Kampi/Watch-DevKit-HW/production/watch-dk-PRELIMINARY/HTML/images/cat_pdf_drill_map_ZSWatch-Watch-DevKit-PTH_drill_map.png

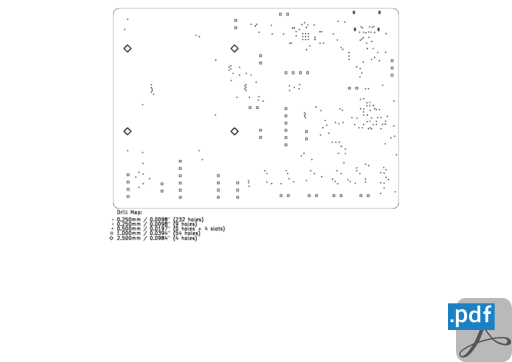
production/watch-dk-PRELIMINARY/HTML/images/cat_pdf_drill_map_ZSWatch-Watch-DevKit-PTH_drill_map.png
