Kampi/Watch-DevKit-HW/production/watch-dk-PRELIMINARY/HTML/images/cat_pdf_schematic_ZSWatch-Watch-DevKit-schematic.png

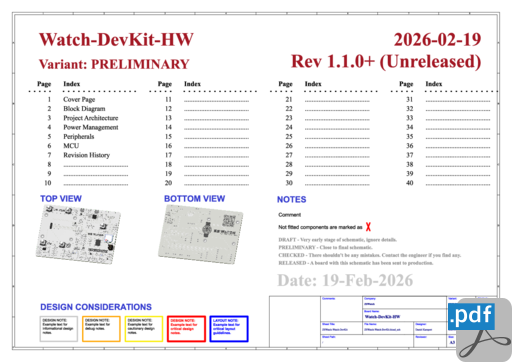
production/watch-dk-PRELIMINARY/HTML/images/cat_pdf_schematic_ZSWatch-Watch-DevKit-schematic.png
