Kampi/Watch-DevKit-HW/production/watch-dk-PRELIMINARY/HTML/images/cat_png_3d_viewer_bottom_ZSWatch-Watch-DevKit-bottom.png

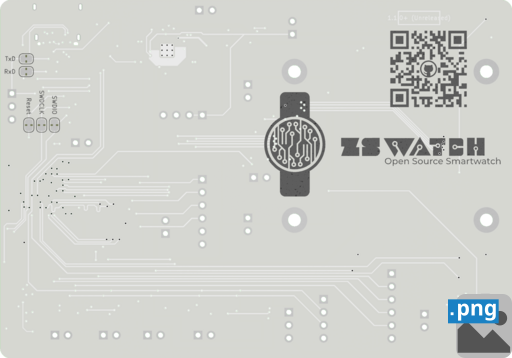
production/watch-dk-PRELIMINARY/HTML/images/cat_png_3d_viewer_bottom_ZSWatch-Watch-DevKit-bottom.png
