Kampi/Watch-DevKit-HW/production/watch-dk-PRELIMINARY/Images/ZSWatch-Watch-DevKit-bottom.png

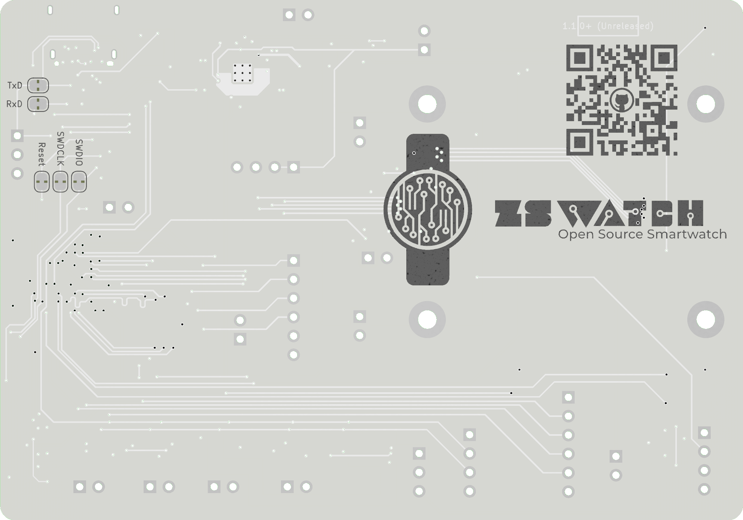
production/watch-dk-PRELIMINARY/Images/ZSWatch-Watch-DevKit-bottom.png
