Kampi/Watch-DevKit-HW/production/watch-dk-RELEASED/HTML/images/cat_png_3d_viewer_bottom_ZSWatch-Watch-DevKit-bottom.png

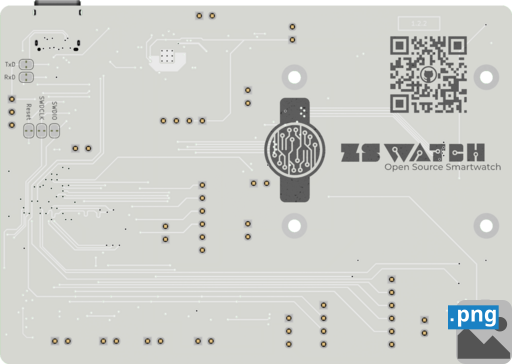
production/watch-dk-RELEASED/HTML/images/cat_png_3d_viewer_bottom_ZSWatch-Watch-DevKit-bottom.png
