Kampi/Watch-DevKit-HW/production/watch-dk-RELEASED/HTML/images/cat_png_3d_viewer_top_ZSWatch-Watch-DevKit-top.png

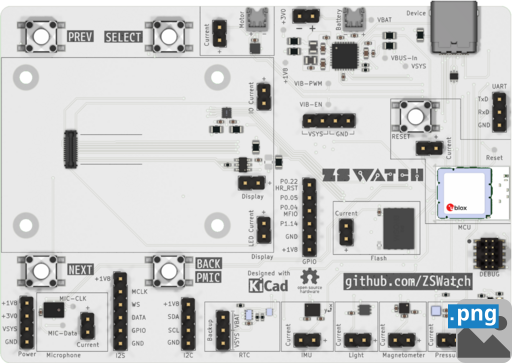
production/watch-dk-RELEASED/HTML/images/cat_png_3d_viewer_top_ZSWatch-Watch-DevKit-top.png
