Kampi/Watch-DevKit-HW/production/watch-dk-RELEASED/Images/ZSWatch-Watch-DevKit-bottom.png

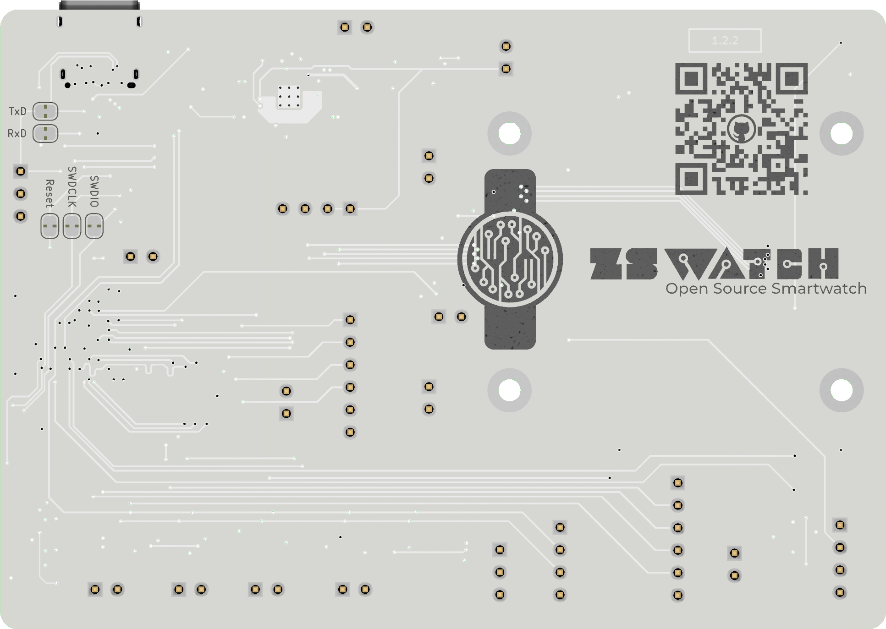
production/watch-dk-RELEASED/Images/ZSWatch-Watch-DevKit-bottom.png
