Kampi/Watch-DevKit-HW/production/watch-dk-PRELIMINARY/Manufacturing/Fabrication/Drill Tables/ZSWatch-Watch-DevKit-(L1-L4)_NPTH_drill_table.csv

Count | Hole Size | Plated | Hole Shape | Drill Layer Pair | Hole Type
1 + 1 | 0.65mm (25.59mils) | NPTH | Round + Slot | F.Cu - B.Cu | Mechanical
Total 2
