Kampi/Watch-DevKit-HW/production/watch-dk-PRELIMINARY/HTML/images/cat_pdf_fabrication_ZSWatch-Watch-DevKit-fabrication.png

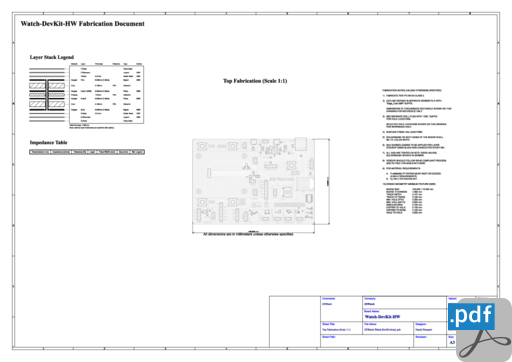
production/watch-dk-PRELIMINARY/HTML/images/cat_pdf_fabrication_ZSWatch-Watch-DevKit-fabrication.png
